emshotton/copperroute/benchmark/reports/plan9-t7t8-vs-java.md

# Comparison: java-current vs rs-main

Created 2026-09-03T23:23:26+00:00 from runs java-278fe14, plan9-t7t8. Config: threads=1 jobs=12 max_passes=10 timeout=300s seeds=1 time metric = cpu_s tier=pcbench

| candidate | version | sha |
|---|---|---|
| java-current | current | `278fe14123c4` |
| rs-main | — | `33b13d26ae10` |

## Overall

- **rs-main** vs java-current: **worse** — 394 wins, 211 losses (107 on hard metrics), 0 ties

## Per tier

| tier | candidate | wins | losses | ties | clean-pass rate | median Δscore | median time ratio |
|---|---|---|---|---|---|---|---|
| all | rs-main | 394 | 211 | 0 | 0.57 | +0.0 | 0.03 |
| d3-a | rs-main | 91 | 52 | 0 | 0.77 | 0.0 | 0.01 |
| d3-b | rs-main | 170 | 90 | 0 | 0.65 | +0.0 | 0.02 |
| d3-c | rs-main | 133 | 69 | 0 | 0.31 | +25.7 | 0.10 |
| pcbench | rs-main | 394 | 211 | 0 | 0.57 | +0.0 | 0.03 |

## Per board

| board | referee | candidate | clean | unrouted | viol | score | Δscore | noise | cpu s | Δcpu s | vias | length mm | verdict |
|---|---|---|---|---|---|---|---|---|---|---|---|---|---|
| pcbench-1-Wire-Wing-pcb_1-Wire_Wing | kicad | java-current | 1.00 | 0 | 0 | 1000.0 | | unmeasured | 46.5 | | 18 | 474.1 | baseline |
| pcbench-1-Wire-Wing-pcb_1-Wire_Wing | kicad | rs-main | 1.00 | 0 | 0 | 1000.0 | +0.0 | | 1.3 | -45.1 | 14 | 470.4 | win (score) |
| pcbench-16x12-bits-I2C_I2C_Servo | kicad | java-current | 0.00 | 0 | 53 | 905.4 | | unmeasured | 53.3 | | 46 | 1039.0 | baseline |
| pcbench-16x12-bits-I2C_I2C_Servo | kicad | rs-main | 1.00 | 0 | 0 | 1000.0 | +94.6 | | 1.6 | -51.7 | 41 | 1039.6 | win (clean_pass_rate) |
| pcbench-1Bitsy_1bitsy | kicad | java-current | 0.00 | 0 | 55 | 931.2 | | unmeasured | 355.2 | | 70 | 1042.8 | baseline |
| pcbench-1Bitsy_1bitsy | kicad | rs-main | 0.00 | 1 | 0 | 993.7 | +62.5 | | 52.5 | -302.7 | 69 | 1029.2 | loss (unrouted) |
| pcbench-2d_conduction_sk9822-matrix | kicad | java-current | 0.00 | 2 | 0 | 994.6 | | unmeasured | 354.9 | | 106 | 2776.3 | baseline |
| pcbench-2d_conduction_sk9822-matrix | kicad | rs-main | 0.00 | 2 | 0 | 994.6 | -0.0 | | 52.0 | -302.9 | 115 | 2768.8 | loss (score) |
| pcbench-4N35-TTL-Serial-Optoisolator_4N35-TTL-Serial-Optoisolator | kicad | java-current | 1.00 | 0 | 0 | 1000.0 | | unmeasured | 17.4 | | 0 | 219.9 | baseline |
| pcbench-4N35-TTL-Serial-Optoisolator_4N35-TTL-Serial-Optoisolator | kicad | rs-main | 1.00 | 0 | 0 | 1000.0 | +0.0 | | 0.2 | -17.3 | 0 | 219.6 | win (score) |
| pcbench-655_testboard | kicad | java-current | 1.00 | 0 | 0 | 1000.0 | | unmeasured | 71.0 | | 27 | 1002.1 | baseline |
| pcbench-655_testboard | kicad | rs-main | 1.00 | 0 | 0 | 1000.0 | +0.0 | | 2.7 | -68.3 | 26 | 1041.8 | win (score) |
| pcbench-6N137-TTL-Serial-Optoisolator_6N137-TTL-Serial-Optoisolator | kicad | java-current | 1.00 | 0 | 0 | 1000.0 | | unmeasured | 44.9 | | 0 | 277.3 | baseline |
| pcbench-6N137-TTL-Serial-Optoisolator_6N137-TTL-Serial-Optoisolator | kicad | rs-main | 0.00 | 1 | 0 | 964.3 | -35.7 | | 0.9 | -44.0 | 0 | 273.0 | loss (clean_pass_rate) |
| pcbench-6volt-5W-solar-cc_6vleadacidsolar | kicad | java-current | 0.00 | 0 | 12 | 980.2 | | unmeasured | 94.8 | | 19 | 949.6 | baseline |
| pcbench-6volt-5W-solar-cc_6vleadacidsolar | kicad | rs-main | 1.00 | 0 | 0 | 1000.0 | +19.8 | | 2.5 | -92.3 | 25 | 885.3 | win (clean_pass_rate) |
| pcbench-74Logic_SA_ADC_SA-ADC | kicad | java-current | 0.00 | 74 | 0 | 834.8 | | unmeasured | 383.7 | | 175 | 2981.5 | baseline |
| pcbench-74Logic_SA_ADC_SA-ADC | kicad | rs-main | 0.00 | 3 | 0 | 993.3 | +158.5 | | 228.2 | -155.4 | 199 | 4529.4 | win (unrouted) |
| pcbench-96boards-sensors_Sensors | kicad | java-current | 0.00 | 14 | 8 | 943.7 | | unmeasured | 394.2 | | 136 | 3334.9 | baseline |
| pcbench-96boards-sensors_Sensors | kicad | rs-main | 0.00 | 3 | 1 | 988.4 | +44.8 | | 112.9 | -281.3 | 157 | 3691.7 | win (unrouted) |
| pcbench-ABOVISP_ABOVISP | kicad | java-current | 0.00 | 1 | 7 | 922.6 | | unmeasured | 55.1 | | 5 | 196.6 | baseline |
| pcbench-ABOVISP_ABOVISP | kicad | rs-main | 1.00 | 0 | 0 | 1000.0 | +77.4 | | 1.1 | -53.9 | 3 | 193.0 | win (clean_pass_rate) |
| pcbench-ADC-PCM4202-SE_ADC-PCM4202-SE | kicad | java-current | 1.00 | 0 | 0 | 1000.0 | | unmeasured | 288.0 | | 41 | 2707.0 | baseline |
| pcbench-ADC-PCM4202-SE_ADC-PCM4202-SE | kicad | rs-main | 1.00 | 0 | 0 | 1000.0 | -0.0 | | 26.1 | -262.0 | 43 | 2641.6 | loss (score) |
| pcbench-APC_AtariPunkConsole | kicad | java-current | 1.00 | 0 | 0 | 1000.0 | | unmeasured | 29.2 | | 2 | 479.1 | baseline |
| pcbench-APC_AtariPunkConsole | kicad | rs-main | 1.00 | 0 | 0 | 1000.0 | -0.0 | | 0.1 | -29.1 | 2 | 484.6 | loss (score) |
| pcbench-APM-RPi-Shield_APM-RPi-Shield | kicad | java-current | 0.00 | 4 | 2 | 964.8 | | unmeasured | 203.5 | | 31 | 1346.1 | baseline |
| pcbench-APM-RPi-Shield_APM-RPi-Shield | kicad | rs-main | 0.00 | 7 | 1 | 942.4 | -22.4 | | 18.4 | -185.2 | 37 | 1180.0 | loss (unrouted) |
| pcbench-AS5043-Encoder_sensor-board | kicad | java-current | 0.00 | 0 | 2 | 986.7 | | unmeasured | 32.3 | | 9 | 249.7 | baseline |
| pcbench-AS5043-Encoder_sensor-board | kicad | rs-main | 1.00 | 0 | 0 | 1000.0 | +13.3 | | 0.3 | -32.0 | 9 | 246.9 | win (clean_pass_rate) |
| pcbench-ATmega32_ExploreUltraAvrDevKit_40pin_AVRMCU | kicad | java-current | 1.00 | 0 | 0 | 1000.0 | | unmeasured | 75.8 | | 7 | 1189.3 | baseline |
| pcbench-ATmega32_ExploreUltraAvrDevKit_40pin_AVRMCU | kicad | rs-main | 0.00 | 1 | 0 | 987.5 | -12.5 | | 3.2 | -72.6 | 7 | 1138.8 | loss (clean_pass_rate) |
| pcbench-ATtiny461Breakout_ATTiny461DevBoard | kicad | java-current | 0.00 | 1 | 2 | 963.2 | | unmeasured | 65.3 | | 3 | 296.4 | baseline |
| pcbench-ATtiny461Breakout_ATTiny461DevBoard | kicad | rs-main | 0.00 | 0 | 1 | 994.7 | +31.6 | | 0.2 | -65.1 | 3 | 283.5 | win (unrouted) |
| pcbench-AVR-ISP_level-shifter_AVR-ISP_level-shifter | kicad | java-current | 0.00 | 1 | 4 | 972.7 | | unmeasured | 83.2 | | 8 | 366.9 | baseline |
| pcbench-AVR-ISP_level-shifter_AVR-ISP_level-shifter | kicad | rs-main | 1.00 | 0 | 0 | 1000.0 | +27.3 | | 1.0 | -82.2 | 4 | 371.2 | win (clean_pass_rate) |
| pcbench-AVR-ISP_pogo-plug_1.27mm_AVR-ISP_pogo-plug_1.27mm | kicad | java-current | 1.00 | 0 | 0 | 1000.0 | | unmeasured | 44.2 | | 1 | 48.8 | baseline |
| pcbench-AVR-ISP_pogo-plug_1.27mm_AVR-ISP_pogo-plug_1.27mm | kicad | rs-main | 1.00 | 0 | 0 | 1000.0 | -0.0 | | 0.6 | -43.6 | 1 | 48.8 | loss (score) |
| pcbench-AVR-Playground_hello_world | kicad | java-current | 0.00 | 1 | 0 | 800.0 | | unmeasured | 26.6 | | 0 | 108.5 | baseline |
| pcbench-AVR-Playground_hello_world | kicad | rs-main | 0.00 | 1 | 0 | 800.0 | 0.0 | | 0.1 | -26.5 | 0 | 108.5 | win (cpu_s) |
| pcbench-AVR-ZIF-Programmer_AVR-ZIF-Prog | kicad | java-current | 1.00 | 0 | 0 | 1000.0 | | unmeasured | 104.0 | | 8 | 1490.5 | baseline |
| pcbench-AVR-ZIF-Programmer_AVR-ZIF-Prog | kicad | rs-main | 1.00 | 0 | 0 | 1000.0 | +0.0 | | 1.9 | -102.1 | 6 | 1502.7 | win (score) |
| pcbench-Amiga-A1012-PCB_Amiga-A1012 | kicad | java-current | 0.00 | 0 | 42 | 913.4 | | unmeasured | 107.4 | | 47 | 1745.1 | baseline |
| pcbench-Amiga-A1012-PCB_Amiga-A1012 | kicad | rs-main | 1.00 | 0 | 0 | 1000.0 | +86.6 | | 4.6 | -102.7 | 46 | 1764.4 | win (clean_pass_rate) |
| pcbench-AmpOne_dev-AmpOne | kicad | java-current | 0.00 | 1 | 0 | 996.9 | | unmeasured | 293.2 | | 60 | 2688.2 | baseline |
| pcbench-AmpOne_dev-AmpOne | kicad | rs-main | 1.00 | 0 | 0 | 1000.0 | +3.1 | | 18.2 | -275.0 | 46 | 2723.2 | win (clean_pass_rate) |
| pcbench-AnalogThermometer_AnalogThermometer | kicad | java-current | 0.00 | 0 | 3 | 982.9 | | unmeasured | 36.6 | | 2 | 208.7 | baseline |
| pcbench-AnalogThermometer_AnalogThermometer | kicad | rs-main | 1.00 | 0 | 0 | 1000.0 | +17.1 | | 0.4 | -36.2 | 4 | 207.6 | win (clean_pass_rate) |
| pcbench-Apple-M0110-BT_Apple M0110 | kicad | java-current | 1.00 | 0 | 0 | 1000.0 | | unmeasured | 155.5 | | 0 | 4384.2 | baseline |
| pcbench-Apple-M0110-BT_Apple M0110 | kicad | rs-main | 1.00 | 0 | 0 | 1000.0 | +0.0 | | 4.6 | -150.9 | 0 | 4364.1 | win (score) |
| pcbench-Arduino-Theremin_arduino-theremin-v1 | kicad | java-current | 0.00 | 1 | 0 | 963.0 | | unmeasured | 50.1 | | 3 | 596.6 | baseline |
| pcbench-Arduino-Theremin_arduino-theremin-v1 | kicad | rs-main | 0.00 | 2 | 0 | 925.9 | -37.0 | | 1.5 | -48.7 | 3 | 552.8 | loss (unrouted) |
| pcbench-Arduino_Lipo_Storage_Discharger_Lipo_Storage_Discharger | kicad | java-current | 1.00 | 0 | 0 | 1000.0 | | unmeasured | 64.0 | | 7 | 1041.8 | baseline |
| pcbench-Arduino_Lipo_Storage_Discharger_Lipo_Storage_Discharger | kicad | rs-main | 1.00 | 0 | 0 | 1000.0 | -0.0 | | 1.9 | -62.0 | 13 | 1041.7 | loss (score) |
| pcbench-Atmel-ICE-Header-Adapter_ice header adapter pcb | kicad | java-current | 0.00 | 3 | 0 | 957.7 | | unmeasured | 137.7 | | 0 | 970.9 | baseline |
| pcbench-Atmel-ICE-Header-Adapter_ice header adapter pcb | kicad | rs-main | 0.00 | 3 | 0 | 957.7 | +0.0 | | 5.7 | -132.0 | 0 | 916.2 | win (score) |
| pcbench-Avem_Hardware_Avem_demo | kicad | java-current | 0.00 | 1 | 39 | 890.0 | | unmeasured | 148.2 | | 16 | 656.7 | baseline |
| pcbench-Avem_Hardware_Avem_demo | kicad | rs-main | 1.00 | 0 | 0 | 1000.0 | +110.0 | | 2.6 | -145.6 | 20 | 717.4 | win (clean_pass_rate) |
| pcbench-AzizLight_AzizLight | kicad | java-current | 0.00 | 0 | 23 | 954.9 | | unmeasured | 93.0 | | 35 | 722.5 | baseline |
| pcbench-AzizLight_AzizLight | kicad | rs-main | 0.00 | 1 | 0 | 990.2 | +35.3 | | 4.6 | -88.5 | 45 | 704.6 | loss (unrouted) |
| pcbench-BB-PWR-3608_BB-PWR-3608_revA | kicad | java-current | 1.00 | 0 | 0 | 1000.0 | | unmeasured | 49.1 | | 3 | 94.3 | baseline |
| pcbench-BB-PWR-3608_BB-PWR-3608_revA | kicad | rs-main | 1.00 | 0 | 0 | 1000.0 | +0.0 | | 1.6 | -47.6 | 3 | 81.8 | win (score) |
| pcbench-BB-PWR-8009_BB-PWR-8009_revA | kicad | java-current | 1.00 | 0 | 0 | 1000.0 | | unmeasured | 59.9 | | 2 | 72.3 | baseline |
| pcbench-BB-PWR-8009_BB-PWR-8009_revA | kicad | rs-main | 1.00 | 0 | 0 | 1000.0 | +0.0 | | 1.0 | -58.9 | 0 | 76.3 | win (score) |
| pcbench-BLDC-controller_BLDC_controller | kicad | java-current | 0.00 | 134 | 46 | 674.5 | | unmeasured | 357.1 | | 44 | 863.4 | baseline |
| pcbench-BLDC-controller_BLDC_controller | kicad | rs-main | 0.00 | 18 | 1 | 958.6 | +284.1 | | 171.2 | -185.9 | 45 | 1285.6 | win (unrouted) |
| pcbench-BML-Badges_BML-Badges | kicad | java-current | 1.00 | 0 | 0 | 1000.0 | | unmeasured | 27.0 | | 0 | 460.8 | baseline |
| pcbench-BML-Badges_BML-Badges | kicad | rs-main | 1.00 | 0 | 0 | 1000.0 | -0.0 | | 0.1 | -26.8 | 0 | 470.8 | loss (score) |
| pcbench-BML-Badges_BML_01 | kicad | java-current | 1.00 | 0 | 0 | 1000.0 | | unmeasured | 19.9 | | 0 | 339.9 | baseline |
| pcbench-BML-Badges_BML_01 | kicad | rs-main | 1.00 | 0 | 0 | 1000.0 | -0.0 | | 0.2 | -19.7 | 0 | 346.2 | loss (score) |
| pcbench-Baofeng-Interface_BaofengInterfaceIsolated | kicad | java-current | 1.00 | 0 | 0 | 1000.0 | | unmeasured | 67.2 | | 0 | 668.8 | baseline |
| pcbench-Baofeng-Interface_BaofengInterfaceIsolated | kicad | rs-main | 1.00 | 0 | 0 | 1000.0 | -0.0 | | 2.3 | -64.9 | 0 | 679.4 | loss (score) |
| pcbench-BirdAttractor_BirdAttractor_RevA | kicad | java-current | 1.00 | 0 | 0 | 1000.0 | | unmeasured | 54.6 | | 2 | 374.0 | baseline |
| pcbench-BirdAttractor_BirdAttractor_RevA | kicad | rs-main | 1.00 | 0 | 0 | 1000.0 | +0.0 | | 3.2 | -51.5 | 2 | 361.4 | win (score) |
| pcbench-BirdAttractor_BirdAttractor_RevC | kicad | java-current | 1.00 | 0 | 0 | 1000.0 | | unmeasured | 68.6 | | 41 | 1085.6 | baseline |
| pcbench-BirdAttractor_BirdAttractor_RevC | kicad | rs-main | 1.00 | 0 | 0 | 1000.0 | +0.0 | | 2.7 | -65.9 | 38 | 1143.1 | win (score) |
| pcbench-BirthdayCakeKeyboard_10Key | kicad | java-current | 0.00 | 0 | 62 | 935.1 | | unmeasured | 269.9 | | 72 | 3894.3 | baseline |
| pcbench-BirthdayCakeKeyboard_10Key | kicad | rs-main | 0.00 | 1 | 0 | 994.8 | +59.7 | | 19.7 | -250.1 | 113 | 3817.4 | loss (unrouted) |
| pcbench-Biscay_Blueeye_mcu | kicad | java-current | 0.00 | 0 | 17 | 946.9 | | unmeasured | 81.0 | | 7 | 1169.7 | baseline |
| pcbench-Biscay_Blueeye_mcu | kicad | rs-main | 1.00 | 0 | 0 | 1000.0 | +53.1 | | 2.5 | -78.5 | 3 | 1232.1 | win (clean_pass_rate) |
| pcbench-Biscay_Blueeye_sipm-fpga | kicad | java-current | 0.00 | 2 | 77 | 884.0 | | unmeasured | 349.4 | | 26 | 1423.5 | baseline |
| pcbench-Biscay_Blueeye_sipm-fpga | kicad | rs-main | 0.00 | 2 | 0 | 986.7 | +102.7 | | 38.7 | -310.7 | 30 | 1371.0 | win (violations) |
| pcbench-Blink-Eras_AVR_ISP_Pogo | kicad | java-current | 1.00 | 0 | 0 | 1000.0 | | unmeasured | 13.5 | | 0 | 97.0 | baseline |
| pcbench-Blink-Eras_AVR_ISP_Pogo | kicad | rs-main | 1.00 | 0 | 0 | 1000.0 | 0.0 | | 0.0 | -13.5 | 0 | 97.0 | win (cpu_s) |
| pcbench-Box0-hv-analog-breakoutboard_breakout | kicad | java-current | 0.00 | 128 | 0 | 174.2 | | unmeasured | 254.5 | | 0 | 98.2 | baseline |
| pcbench-Box0-hv-analog-breakoutboard_breakout | kicad | rs-main | 0.00 | 128 | 0 | 174.2 | 0.0 | | 27.9 | -226.6 | 0 | 98.2 | win (cpu_s) |
| pcbench-Brushless_ESC_Brushless_ESC | kicad | java-current | 0.00 | 1 | 69 | 908.6 | | unmeasured | 171.9 | | 74 | 1377.5 | baseline |
| pcbench-Brushless_ESC_Brushless_ESC | kicad | rs-main | 0.00 | 1 | 14 | 976.5 | +67.9 | | 15.9 | -156.0 | 71 | 1343.1 | win (violations) |
| pcbench-C-BISCUIT_crowbar | kicad | java-current | 0.00 | 0 | 3 | 966.7 | | unmeasured | 22.2 | | 5 | 145.5 | baseline |
| pcbench-C-BISCUIT_crowbar | kicad | rs-main | 1.00 | 0 | 0 | 1000.0 | +33.3 | | 0.2 | -22.0 | 5 | 142.2 | win (clean_pass_rate) |
| pcbench-CAL430FR_CAL430F | kicad | java-current | 0.00 | 8 | 28 | 852.2 | | unmeasured | 375.7 | | 63 | 1012.4 | baseline |
| pcbench-CAL430FR_CAL430F | kicad | rs-main | 0.00 | 8 | 0 | 913.0 | +60.9 | | 67.3 | -308.3 | 62 | 1058.4 | win (violations) |
| pcbench-CAL430FR_CAL430F_watch | kicad | java-current | 0.00 | 0 | 18 | 836.4 | | unmeasured | 52.7 | | 9 | 389.8 | baseline |
| pcbench-CAL430FR_CAL430F_watch | kicad | rs-main | 1.00 | 0 | 0 | 1000.0 | +163.6 | | 1.9 | -50.8 | 8 | 380.8 | win (clean_pass_rate) |
| pcbench-CapPCB_CapPcb | kicad | java-current | 1.00 | 0 | 0 | 1000.0 | | unmeasured | 26.4 | | 0 | 85.3 | baseline |
| pcbench-CapPCB_CapPcb | kicad | rs-main | 1.00 | 0 | 0 | 1000.0 | +0.0 | | 1.2 | -25.2 | 0 | 73.9 | win (score) |
| pcbench-Cherry-Mx-Bitboard_Cherry Mx Bitboard | kicad | java-current | 1.00 | 0 | 0 | 1000.0 | | unmeasured | 12.8 | | 0 | 72.5 | baseline |
| pcbench-Cherry-Mx-Bitboard_Cherry Mx Bitboard | kicad | rs-main | 1.00 | 0 | 0 | 1000.0 | 0.0 | | 0.0 | -12.8 | 0 | 72.5 | win (cpu_s) |
| pcbench-ChirpHardware_chirp | kicad | java-current | 0.00 | 1 | 65 | 860.0 | | unmeasured | 202.8 | | 31 | 763.5 | baseline |
| pcbench-ChirpHardware_chirp | kicad | rs-main | 1.00 | 0 | 0 | 1000.0 | +140.0 | | 56.0 | -146.8 | 25 | 760.2 | win (clean_pass_rate) |
| pcbench-CompactFlashBreakout_CompactFlashBreakout | kicad | java-current | 0.00 | 0 | 1 | 993.9 | | unmeasured | 97.3 | | 16 | 479.8 | baseline |
| pcbench-CompactFlashBreakout_CompactFlashBreakout | kicad | rs-main | 1.00 | 0 | 0 | 1000.0 | +6.1 | | 2.4 | -94.9 | 17 | 460.0 | win (clean_pass_rate) |
| pcbench-CoreOne-xCORE200-Original_CoreOne | kicad | java-current | 0.00 | 302 | 3 | 629.2 | | unmeasured | 366.1 | | 269 | 2530.7 | baseline |
| pcbench-CoreOne-xCORE200-Original_CoreOne | kicad | rs-main | 0.00 | 57 | 1 | 929.9 | +300.7 | | 306.3 | -59.8 | 294 | 5943.2 | win (unrouted) |
| pcbench-CubeSAT-Reaction-Wheel_Edison_Motor_Servo | kicad | java-current | 1.00 | 0 | 0 | 1000.0 | | unmeasured | 16.5 | | 0 | 115.7 | baseline |
| pcbench-CubeSAT-Reaction-Wheel_Edison_Motor_Servo | kicad | rs-main | 1.00 | 0 | 0 | 1000.0 | 0.0 | | 0.1 | -16.3 | 0 | 115.7 | win (cpu_s) |
| pcbench-CubeSAT-Reaction-Wheel__autosave-GPIO to motor | kicad | java-current | 1.00 | 0 | 0 | 1000.0 | | unmeasured | 66.0 | | 3 | 673.2 | baseline |
| pcbench-CubeSAT-Reaction-Wheel__autosave-GPIO to motor | kicad | rs-main | 1.00 | 0 | 0 | 1000.0 | -0.0 | | 0.9 | -65.0 | 4 | 665.3 | loss (score) |
| pcbench-Curryboard_Curryboard | kicad | java-current | 0.00 | 3 | 0 | 980.3 | | unmeasured | 366.6 | | 79 | 1825.5 | baseline |
| pcbench-Curryboard_Curryboard | kicad | rs-main | 0.00 | 1 | 0 | 993.4 | +13.2 | | 43.5 | -323.1 | 70 | 1943.1 | win (unrouted) |
| pcbench-DAC-ADAU1966_DAC-ADAU1966 | kicad | java-current | 0.00 | 102 | 0 | 836.3 | | unmeasured | 374.5 | | 129 | 3150.1 | baseline |
| pcbench-DAC-ADAU1966_DAC-ADAU1966 | kicad | rs-main | 0.00 | 1 | 0 | 998.4 | +162.1 | | 150.7 | -223.8 | 132 | 3914.8 | win (unrouted) |
| pcbench-DC25_DC25 | kicad | java-current | 0.00 | 0 | 25 | 927.5 | | unmeasured | 133.2 | | 46 | 1506.4 | baseline |
| pcbench-DC25_DC25 | kicad | rs-main | 0.00 | 0 | 4 | 988.4 | +60.9 | | 6.5 | -126.7 | 47 | 1449.1 | win (violations) |
| pcbench-DIYDAC_DIYDAC | kicad | java-current | 1.00 | 0 | 0 | 1000.0 | | unmeasured | 17.8 | | 0 | 68.1 | baseline |
| pcbench-DIYDAC_DIYDAC | kicad | rs-main | 1.00 | 0 | 0 | 1000.0 | 0.0 | | 0.1 | -17.7 | 0 | 68.1 | win (cpu_s) |
| pcbench-DPS-1200FB_Adapter_Adapter | kicad | java-current | 0.00 | 1 | 3 | 987.2 | | unmeasured | 88.0 | | 0 | 796.0 | baseline |
| pcbench-DPS-1200FB_Adapter_Adapter | kicad | rs-main | 0.00 | 1 | 3 | 987.2 | +0.0 | | 1.9 | -86.0 | 0 | 794.8 | win (score) |
| pcbench-DaWeather---Project__autosave-CarteDaWeather | kicad | java-current | 1.00 | 0 | 0 | 1000.0 | | unmeasured | 32.4 | | 0 | 594.9 | baseline |
| pcbench-DaWeather---Project__autosave-CarteDaWeather | kicad | rs-main | 0.00 | 0 | 1 | 995.3 | -4.7 | | 0.3 | -32.1 | 0 | 601.2 | loss (clean_pass_rate) |
| pcbench-DasBlinkinput_Das Blinkinput | kicad | java-current | 1.00 | 0 | 0 | 1000.0 | | unmeasured | 340.6 | | 20 | 652.1 | baseline |
| pcbench-DasBlinkinput_Das Blinkinput | kicad | rs-main | 1.00 | 0 | 0 | 1000.0 | +0.0 | | 56.8 | -283.8 | 18 | 668.2 | win (score) |
| pcbench-Dekada_dekada | kicad | java-current | 1.00 | 0 | 0 | 1000.0 | | unmeasured | 148.2 | | 0 | 379.8 | baseline |
| pcbench-Dekada_dekada | kicad | rs-main | 1.00 | 0 | 0 | 1000.0 | +0.0 | | 14.2 | -133.9 | 0 | 379.8 | win (score) |
| pcbench-Dekada_dekada_TopoR_curves | kicad | java-current | 1.00 | 0 | 0 | 1000.0 | | unmeasured | 146.5 | | 0 | 379.8 | baseline |
| pcbench-Dekada_dekada_TopoR_curves | kicad | rs-main | 1.00 | 0 | 0 | 1000.0 | +0.0 | | 8.5 | -138.0 | 0 | 379.8 | win (score) |
| pcbench-DerKnopf_digi-pot | kicad | java-current | 0.00 | 1 | 54 | 821.2 | | unmeasured | 204.7 | | 29 | 462.4 | baseline |
| pcbench-DerKnopf_digi-pot | kicad | rs-main | 0.00 | 2 | 0 | 969.7 | +148.5 | | 10.9 | -193.8 | 27 | 463.2 | loss (unrouted) |
| pcbench-DerKnopf_led-ring | kicad | java-current | 0.00 | 0 | 4 | 988.4 | | unmeasured | 206.5 | | 45 | 569.4 | baseline |
| pcbench-DerKnopf_led-ring | kicad | rs-main | 1.00 | 0 | 0 | 1000.0 | +11.6 | | 11.0 | -195.5 | 44 | 557.8 | win (clean_pass_rate) |
| pcbench-DerKnopf_power-supply | kicad | java-current | 1.00 | 0 | 0 | 1000.0 | | unmeasured | 70.1 | | 1 | 185.7 | baseline |
| pcbench-DerKnopf_power-supply | kicad | rs-main | 1.00 | 0 | 0 | 1000.0 | -0.0 | | 1.5 | -68.6 | 1 | 188.9 | loss (score) |
| pcbench-DiscoDanceFloorV1_DiscoDongle | kicad | java-current | 0.00 | 0 | 11 | 958.5 | | unmeasured | 284.7 | | 10 | 519.2 | baseline |
| pcbench-DiscoDanceFloorV1_DiscoDongle | kicad | rs-main | 1.00 | 0 | 0 | 1000.0 | +41.5 | | 16.4 | -268.3 | 6 | 550.6 | win (clean_pass_rate) |
| pcbench-DoroidOscillo-Board_Android_Oscilloscope | kicad | java-current | 0.00 | 13 | 67 | 914.6 | | unmeasured | 336.3 | | 102 | 1636.5 | baseline |
| pcbench-DoroidOscillo-Board_Android_Oscilloscope | kicad | rs-main | 0.00 | 6 | 0 | 980.6 | +66.0 | | 137.8 | -198.5 | 96 | 1753.4 | win (unrouted) |
| pcbench-DualLM317BenchSupply_DualLM317BenchSupply | kicad | java-current | 1.00 | 0 | 0 | 1000.0 | | unmeasured | 101.3 | | 0 | 1139.7 | baseline |
| pcbench-DualLM317BenchSupply_DualLM317BenchSupply | kicad | rs-main | 1.00 | 0 | 0 | 1000.0 | -0.0 | | 4.6 | -96.7 | 0 | 1142.6 | loss (score) |
| pcbench-DustSensorShield_DustSensorShield | kicad | java-current | 0.00 | 1 | 0 | 941.2 | | unmeasured | 69.4 | | 6 | 467.2 | baseline |
| pcbench-DustSensorShield_DustSensorShield | kicad | rs-main | 0.00 | 1 | 0 | 941.2 | -0.0 | | 1.2 | -68.2 | 12 | 453.3 | loss (score) |
| pcbench-E202VAR-Natural-Radio-Receiver_e202var-vlf-radio-receiver | kicad | java-current | 0.00 | 1 | 0 | 989.1 | | unmeasured | 77.6 | | 1 | 961.2 | baseline |
| pcbench-E202VAR-Natural-Radio-Receiver_e202var-vlf-radio-receiver | kicad | rs-main | 0.00 | 1 | 0 | 989.1 | -0.0 | | 2.7 | -74.9 | 1 | 990.2 | loss (score) |
| pcbench-ESP-12-breakout_ESP12E-breakout | kicad | java-current | 1.00 | 0 | 0 | 1000.0 | | unmeasured | 47.7 | | 9 | 310.7 | baseline |
| pcbench-ESP-12-breakout_ESP12E-breakout | kicad | rs-main | 1.00 | 0 | 0 | 1000.0 | +0.0 | | 0.5 | -47.2 | 7 | 316.0 | win (score) |
| pcbench-ESP-Breakout_ESP-Breakout | kicad | java-current | 1.00 | 0 | 0 | 1000.0 | | unmeasured | 41.5 | | 18 | 350.8 | baseline |
| pcbench-ESP-Breakout_ESP-Breakout | kicad | rs-main | 1.00 | 0 | 0 | 1000.0 | +0.0 | | 0.4 | -41.1 | 17 | 360.1 | win (score) |
| pcbench-ESP07-Breakout_ESP07-Breakout | kicad | java-current | 0.00 | 2 | 0 | 969.2 | | unmeasured | 116.8 | | 10 | 702.2 | baseline |
| pcbench-ESP07-Breakout_ESP07-Breakout | kicad | rs-main | 0.00 | 3 | 3 | 944.6 | -24.6 | | 4.0 | -112.9 | 11 | 717.6 | loss (unrouted) |
| pcbench-ESP32-Module-Breakout_ESP32S-breakout | kicad | java-current | 0.00 | 0 | 13 | 943.5 | | unmeasured | 83.6 | | 27 | 750.3 | baseline |
| pcbench-ESP32-Module-Breakout_ESP32S-breakout | kicad | rs-main | 1.00 | 0 | 0 | 1000.0 | +56.5 | | 2.0 | -81.7 | 29 | 745.2 | win (clean_pass_rate) |
| pcbench-ESP8266-MQTT-battery-monitor-hw_battery-monitor | kicad | java-current | 0.00 | 0 | 27 | 943.2 | | unmeasured | 87.5 | | 25 | 645.7 | baseline |
| pcbench-ESP8266-MQTT-battery-monitor-hw_battery-monitor | kicad | rs-main | 0.00 | 1 | 0 | 989.5 | +46.3 | | 5.3 | -82.2 | 24 | 622.0 | loss (unrouted) |
| pcbench-ESPLux_Board | kicad | java-current | 1.00 | 0 | 0 | 1000.0 | | unmeasured | 270.2 | | 10 | 789.9 | baseline |
| pcbench-ESPLux_Board | kicad | rs-main | 0.00 | 1 | 0 | 981.5 | -18.5 | | 4.3 | -266.0 | 26 | 795.1 | loss (clean_pass_rate) |
| pcbench-ESP_BaPoTeSta_ESP_BaPoTeSta | kicad | java-current | 0.00 | 2 | 0 | 981.5 | | unmeasured | 166.0 | | 32 | 791.0 | baseline |
| pcbench-ESP_BaPoTeSta_ESP_BaPoTeSta | kicad | rs-main | 0.00 | 9 | 0 | 916.7 | -64.8 | | 13.2 | -152.8 | 16 | 699.5 | loss (unrouted) |
| pcbench-ESP_WiFiSwitch_WifiSwitch | kicad | java-current | 0.00 | 0 | 1 | 990.9 | | unmeasured | 37.6 | | 6 | 323.1 | baseline |
| pcbench-ESP_WiFiSwitch_WifiSwitch | kicad | rs-main | 1.00 | 0 | 0 | 1000.0 | +9.1 | | 0.3 | -37.2 | 7 | 320.7 | win (clean_pass_rate) |
| pcbench-Eggbot-Spherebot-polargraph-Controller_eggbot-spherebot-polargraph-controller | kicad | java-current | 1.00 | 0 | 0 | 1000.0 | | unmeasured | 56.5 | | 3 | 1268.6 | baseline |
| pcbench-Eggbot-Spherebot-polargraph-Controller_eggbot-spherebot-polargraph-controller | kicad | rs-main | 1.00 | 0 | 0 | 1000.0 | -0.0 | | 0.8 | -55.6 | 4 | 1270.7 | loss (score) |
| pcbench-Electronics-MainBoard_MainBoard | kicad | java-current | 0.00 | 1 | 42 | 967.0 | | unmeasured | 336.6 | | 84 | 2899.8 | baseline |
| pcbench-Electronics-MainBoard_MainBoard | kicad | rs-main | 0.00 | 1 | 0 | 996.5 | +29.5 | | 26.2 | -310.4 | 85 | 2898.4 | win (violations) |
| pcbench-EncoderBoard_Enc_Pan_Led | kicad | java-current | 0.00 | 7 | 26 | 874.2 | | unmeasured | 349.3 | | 38 | 840.4 | baseline |
| pcbench-EncoderBoard_Enc_Pan_Led | kicad | rs-main | 0.00 | 11 | 0 | 886.6 | +12.4 | | 27.2 | -322.1 | 26 | 743.3 | loss (unrouted) |
| pcbench-FRM16_Relay_Module_I2C_Controller_relay_controller | kicad | java-current | 0.00 | 0 | 3 | 989.1 | | unmeasured | 302.2 | | 52 | 1478.1 | baseline |
| pcbench-FRM16_Relay_Module_I2C_Controller_relay_controller | kicad | rs-main | 0.00 | 1 | 0 | 981.8 | -7.3 | | 8.3 | -293.9 | 61 | 1532.8 | loss (unrouted) |
| pcbench-FT231X_breakout_FTDI_FT231XS-U_Breakout | kicad | java-current | 0.00 | 3 | 3 | 910.0 | | unmeasured | 130.3 | | 17 | 371.3 | baseline |
| pcbench-FT231X_breakout_FTDI_FT231XS-U_Breakout | kicad | rs-main | 0.00 | 1 | 0 | 975.0 | +65.0 | | 3.8 | -126.5 | 16 | 400.0 | win (unrouted) |
| pcbench-FlashProgrammer_flash_programmer | kicad | java-current | 0.00 | 5 | 52 | 890.8 | | unmeasured | 331.7 | | 60 | 1453.3 | baseline |
| pcbench-FlashProgrammer_flash_programmer | kicad | rs-main | 0.00 | 4 | 0 | 971.6 | +80.9 | | 24.1 | -307.6 | 56 | 1441.7 | win (unrouted) |
| pcbench-FogDrive_attiny45_slim | kicad | java-current | 1.00 | 0 | 0 | 1000.0 | | unmeasured | 17.9 | | 0 | 52.5 | baseline |
| pcbench-FogDrive_attiny45_slim | kicad | rs-main | 1.00 | 0 | 0 | 1000.0 | 0.0 | | 0.1 | -17.8 | 0 | 52.5 | win (cpu_s) |
| pcbench-HES-V2__autosave-hes | kicad | java-current | 1.00 | 0 | 0 | 1000.0 | | unmeasured | 30.7 | | 0 | 456.9 | baseline |
| pcbench-HES-V2__autosave-hes | kicad | rs-main | 1.00 | 0 | 0 | 1000.0 | +0.0 | | 0.1 | -30.6 | 0 | 456.2 | win (score) |
| pcbench-HES-V2_hes | kicad | java-current | 1.00 | 0 | 0 | 1000.0 | | unmeasured | 30.0 | | 0 | 456.9 | baseline |
| pcbench-HES-V2_hes | kicad | rs-main | 1.00 | 0 | 0 | 1000.0 | +0.0 | | 0.1 | -29.9 | 0 | 456.2 | win (score) |
| pcbench-HW-AC-Emeter_ac-power-monitor | kicad | java-current | 0.00 | 1 | 13 | 966.3 | | unmeasured | 157.8 | | 37 | 1110.7 | baseline |
| pcbench-HW-AC-Emeter_ac-power-monitor | kicad | rs-main | 1.00 | 0 | 0 | 1000.0 | +33.6 | | 5.9 | -151.9 | 35 | 1196.2 | win (clean_pass_rate) |
| pcbench-Hangul-Clock_Hangul | kicad | java-current | 0.00 | 0 | 28 | 973.2 | | unmeasured | 274.8 | | 73 | 3221.7 | baseline |
| pcbench-Hangul-Clock_Hangul | kicad | rs-main | 1.00 | 0 | 0 | 1000.0 | +26.8 | | 18.4 | -256.4 | 81 | 3240.4 | win (clean_pass_rate) |
| pcbench-Hardware-done-with-kicad_AVRlearn | kicad | java-current | 0.00 | 0 | 3 | 976.0 | | unmeasured | 29.9 | | 8 | 415.6 | baseline |
| pcbench-Hardware-done-with-kicad_AVRlearn | kicad | rs-main | 1.00 | 0 | 0 | 1000.0 | +24.0 | | 0.3 | -29.6 | 7 | 424.8 | win (clean_pass_rate) |
| pcbench-Hardware_Playground_BL_PCB_latest | kicad | java-current | 0.00 | 0 | 24 | 979.9 | | unmeasured | 158.5 | | 16 | 1888.5 | baseline |
| pcbench-Hardware_Playground_BL_PCB_latest | kicad | rs-main | 1.00 | 0 | 0 | 1000.0 | +20.1 | | 9.3 | -149.1 | 16 | 1865.9 | win (clean_pass_rate) |
| pcbench-Hardware_Playground_Touch_Switch_1ch_PCB | kicad | java-current | 0.00 | 1 | 19 | 955.1 | | unmeasured | 285.4 | | 29 | 668.1 | baseline |
| pcbench-Hardware_Playground_Touch_Switch_1ch_PCB | kicad | rs-main | 0.00 | 3 | 0 | 972.0 | +16.8 | | 24.9 | -260.6 | 28 | 711.8 | loss (unrouted) |
| pcbench-Hardware_Playground_buck_led_driver | kicad | java-current | 0.00 | 1 | 0 | 944.4 | | unmeasured | 34.8 | | 3 | 104.1 | baseline |
| pcbench-Hardware_Playground_buck_led_driver | kicad | rs-main | 0.00 | 1 | 0 | 944.4 | -0.0 | | 0.4 | -34.4 | 3 | 105.2 | loss (score) |
| pcbench-Hardware_Playground_esp8266_uno_relay | kicad | java-current | 0.00 | 1 | 0 | 994.9 | | unmeasured | 116.6 | | 1 | 580.2 | baseline |
| pcbench-Hardware_Playground_esp8266_uno_relay | kicad | rs-main | 0.00 | 1 | 0 | 994.9 | -0.0 | | 5.8 | -110.8 | 1 | 594.5 | loss (score) |
| pcbench-Hardware_Playground_hy_adapter | kicad | java-current | 1.00 | 0 | 0 | 1000.0 | | unmeasured | 67.3 | | 7 | 73.1 | baseline |
| pcbench-Hardware_Playground_hy_adapter | kicad | rs-main | 1.00 | 0 | 0 | 1000.0 | -0.0 | | 1.9 | -65.4 | 9 | 62.1 | loss (score) |
| pcbench-Hardware_Playground_minimal_node_rfm69w | kicad | java-current | 0.00 | 9 | 8 | 897.1 | | unmeasured | 263.8 | | 22 | 473.1 | baseline |
| pcbench-Hardware_Playground_minimal_node_rfm69w | kicad | rs-main | 0.00 | 6 | 0 | 941.7 | +44.7 | | 17.0 | -246.8 | 30 | 526.9 | win (unrouted) |
| pcbench-Hardware_Playground_nrf52832_uno | kicad | java-current | 0.00 | 4 | 36 | 883.3 | | unmeasured | 280.3 | | 27 | 1402.3 | baseline |
| pcbench-Hardware_Playground_nrf52832_uno | kicad | rs-main | 0.00 | 5 | 0 | 947.9 | +64.6 | | 22.6 | -257.7 | 33 | 1432.8 | loss (unrouted) |
| pcbench-Hardware_Playground_orange_pi_zero_node | kicad | java-current | 0.00 | 1 | 2 | 993.1 | | unmeasured | 153.1 | | 1 | 781.5 | baseline |
| pcbench-Hardware_Playground_orange_pi_zero_node | kicad | rs-main | 0.00 | 1 | 1 | 994.1 | +1.0 | | 10.0 | -143.1 | 1 | 779.2 | win (violations) |
| pcbench-Hardware_Playground_pro_mini | kicad | java-current | 0.00 | 1 | 0 | 987.2 | | unmeasured | 131.0 | | 4 | 462.4 | baseline |
| pcbench-Hardware_Playground_pro_mini | kicad | rs-main | 0.00 | 3 | 0 | 961.5 | -25.6 | | 7.2 | -123.9 | 5 | 417.9 | loss (unrouted) |
| pcbench-Hardware_Playground_rpi_zero | kicad | java-current | 0.00 | 2 | 21 | 971.4 | | unmeasured | 193.6 | | 11 | 845.8 | baseline |
| pcbench-Hardware_Playground_rpi_zero | kicad | rs-main | 0.00 | 1 | 13 | 983.4 | +12.0 | | 16.8 | -176.7 | 14 | 867.1 | win (unrouted) |
| pcbench-Hardware_Playground_serial_gw_ATMEGA328P | kicad | java-current | 0.00 | 1 | 57 | 928.7 | | unmeasured | 338.0 | | 44 | 779.4 | baseline |
| pcbench-Hardware_Playground_serial_gw_ATMEGA328P | kicad | rs-main | 0.00 | 1 | 10 | 982.8 | +54.0 | | 40.3 | -297.7 | 34 | 778.9 | win (violations) |
| pcbench-Hardware_Playground_serial_gw_maple_mini | kicad | java-current | 1.00 | 0 | 0 | 1000.0 | | unmeasured | 125.3 | | 7 | 925.2 | baseline |
| pcbench-Hardware_Playground_serial_gw_maple_mini | kicad | rs-main | 1.00 | 0 | 0 | 1000.0 | +0.0 | | 6.1 | -119.2 | 6 | 924.0 | win (score) |
| pcbench-Hardware_Playground_usb_shield | kicad | java-current | 1.00 | 0 | 0 | 1000.0 | | unmeasured | 126.7 | | 0 | 703.6 | baseline |
| pcbench-Hardware_Playground_usb_shield | kicad | rs-main | 0.00 | 1 | 0 | 995.3 | -4.7 | | 13.0 | -113.7 | 1 | 673.2 | loss (clean_pass_rate) |
| pcbench-Hardware_Playground_wifi_lights | kicad | java-current | 1.00 | 0 | 0 | 1000.0 | | unmeasured | 70.7 | | 8 | 628.4 | baseline |
| pcbench-Hardware_Playground_wifi_lights | kicad | rs-main | 1.00 | 0 | 0 | 1000.0 | +0.0 | | 0.8 | -69.8 | 7 | 617.0 | win (score) |
| pcbench-HaveSome_PCB_HaveSomePCB | kicad | java-current | 0.00 | 1 | 0 | 956.5 | | unmeasured | 66.7 | | 0 | 74.2 | baseline |
| pcbench-HaveSome_PCB_HaveSomePCB | kicad | rs-main | 1.00 | 0 | 0 | 1000.0 | +43.5 | | 1.6 | -65.1 | 1 | 82.9 | win (clean_pass_rate) |
| pcbench-HellScribe_HellScribe | kicad | java-current | 0.00 | 0 | 25 | 946.2 | | unmeasured | 105.8 | | 47 | 1541.4 | baseline |
| pcbench-HellScribe_HellScribe | kicad | rs-main | 1.00 | 0 | 0 | 1000.0 | +53.8 | | 4.6 | -101.2 | 44 | 1562.3 | win (clean_pass_rate) |
| pcbench-HillhacksLantern_LEDLantern | kicad | java-current | 0.00 | 2 | 0 | 928.6 | | unmeasured | 52.0 | | 2 | 379.4 | baseline |
| pcbench-HillhacksLantern_LEDLantern | kicad | rs-main | 0.00 | 3 | 0 | 892.9 | -35.7 | | 1.2 | -50.8 | 3 | 379.2 | loss (unrouted) |
| pcbench-Hypfer-RGB-W-LED-Controller_led_strip_controller | kicad | java-current | 0.00 | 1 | 0 | 986.5 | | unmeasured | 88.3 | | 0 | 1093.1 | baseline |
| pcbench-Hypfer-RGB-W-LED-Controller_led_strip_controller | kicad | rs-main | 1.00 | 0 | 0 | 1000.0 | +13.5 | | 2.0 | -86.3 | 0 | 1199.6 | win (clean_pass_rate) |
| pcbench-I2CTempsensor_sensors | kicad | java-current | 1.00 | 0 | 0 | 1000.0 | | unmeasured | 16.2 | | 0 | 142.5 | baseline |
| pcbench-I2CTempsensor_sensors | kicad | rs-main | 1.00 | 0 | 0 | 1000.0 | -0.0 | | 0.1 | -16.1 | 0 | 152.9 | loss (score) |
| pcbench-ID-FIX_scanConnect | kicad | java-current | 1.00 | 0 | 0 | 1000.0 | | unmeasured | 12.5 | | 0 | 50.5 | baseline |
| pcbench-ID-FIX_scanConnect | kicad | rs-main | 1.00 | 0 | 0 | 1000.0 | -0.0 | | 0.0 | -12.5 | 0 | 51.9 | loss (score) |
| pcbench-IR-Transponder-ATTiny85-v2_Transponder_v2 | kicad | java-current | 0.00 | 1 | 0 | 952.4 | | unmeasured | 31.4 | | 3 | 130.4 | baseline |
| pcbench-IR-Transponder-ATTiny85-v2_Transponder_v2 | kicad | rs-main | 0.00 | 1 | 0 | 952.4 | +0.0 | | 0.8 | -30.6 | 2 | 121.8 | win (score) |
| pcbench-ISO-port_ch340-usb-serial-isolated | kicad | java-current | 0.00 | 1 | 0 | 987.3 | | unmeasured | 101.5 | | 20 | 661.3 | baseline |
| pcbench-ISO-port_ch340-usb-serial-isolated | kicad | rs-main | 0.00 | 1 | 0 | 987.3 | +0.0 | | 9.2 | -92.2 | 20 | 645.5 | win (score) |
| pcbench-Inhibition_amplifier | kicad | java-current | 1.00 | 0 | 0 | 1000.0 | | unmeasured | 243.2 | | 9 | 2386.8 | baseline |
| pcbench-Inhibition_amplifier | kicad | rs-main | 0.00 | 2 | 0 | 986.7 | -13.3 | | 6.8 | -236.3 | 8 | 2237.0 | loss (clean_pass_rate) |
| pcbench-Inkjet_InkjetBreakout | kicad | java-current | 0.00 | 0 | 21 | 676.9 | | unmeasured | 27.0 | | 3 | 252.6 | baseline |
| pcbench-Inkjet_InkjetBreakout | kicad | rs-main | 1.00 | 0 | 0 | 1000.0 | +323.1 | | 0.2 | -26.8 | 3 | 254.7 | win (clean_pass_rate) |
| pcbench-Inkjet_InkjetDriver | kicad | java-current | 0.00 | 0 | 6 | 981.5 | | unmeasured | 83.1 | | 28 | 1179.4 | baseline |
| pcbench-Inkjet_InkjetDriver | kicad | rs-main | 1.00 | 0 | 0 | 1000.0 | +18.5 | | 2.3 | -80.8 | 30 | 1201.5 | win (clean_pass_rate) |
| pcbench-Inkjet_PiezoDriver | kicad | java-current | 0.00 | 1 | 9 | 903.4 | | unmeasured | 61.4 | | 9 | 265.7 | baseline |
| pcbench-Inkjet_PiezoDriver | kicad | rs-main | 0.00 | 1 | 0 | 965.5 | +62.1 | | 3.5 | -57.9 | 7 | 258.9 | win (violations) |
| pcbench-Inkjet__autosave-InkjetDriver | kicad | java-current | 0.00 | 0 | 6 | 981.5 | | unmeasured | 85.0 | | 28 | 1179.4 | baseline |
| pcbench-Inkjet__autosave-InkjetDriver | kicad | rs-main | 1.00 | 0 | 0 | 1000.0 | +18.5 | | 3.6 | -81.4 | 30 | 1201.5 | win (clean_pass_rate) |
| pcbench-JLink-SWD_JLink-SWD | kicad | java-current | 1.00 | 0 | 0 | 1000.0 | | unmeasured | 44.7 | | 4 | 298.0 | baseline |
| pcbench-JLink-SWD_JLink-SWD | kicad | rs-main | 1.00 | 0 | 0 | 1000.0 | -0.0 | | 0.6 | -44.0 | 5 | 304.6 | loss (score) |
| pcbench-Kefersender_UKW TX | kicad | java-current | 0.00 | 6 | 8 | 912.6 | | unmeasured | 135.6 | | 0 | 416.9 | baseline |
| pcbench-Kefersender_UKW TX | kicad | rs-main | 0.00 | 6 | 0 | 931.0 | +18.4 | | 9.7 | -125.9 | 0 | 393.5 | win (violations) |
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
