emshotton/copperroute/crates/copper-drc/tests/data/solder-mask-unnumbered-pads/README.md

# Logical pad identity oracle

Both physical pads have empty pad numbers in the same footprint; they are not one logical pad. Both are unnetted. KiCad 10.0.6 reports 1 mask bridges. Derived from solder-mask-pad-pad with net assignments removed and pad numbers changed.

```sh
kicad-cli pcb drc --format json --all-track-errors -o drc.json mask.kicad_pcb
```

The Rust test models the browser adapter splitting physical pads into independently placed components, preserving their source footprint and source pad number.
