emshotton/copperroute/tests/reference-frozen/java-head-2026-09/router-dac2020-bm01/router-steps18.meta.txt

jar          <FREEROUTING_JAVA_DIR>/build/libs/freerouting-current-executable.jar
jar size     63288652 bytes
jar mtime    2026-08-29 08:05:35 -0700
jar version  Freerouting 2.3.1-SNAPSHOT
java         openjdk version "25.0.4.1" 2026-08-18
hash mode    -XX:hashCode=2
driver       <workspace>/scripts/differential/java/P6T1.java --steps=1-8
connections  294
command      java -Djava.awt.headless=true -Duser.language=en -Duser.country=US -XX:+UnlockExperimentalVMOptions -XX:hashCode=2 -cp <classes>:<jar> app.freerouting.autoroute.maze.P6T1 <FREEROUTING_JAVA_DIR>/fixtures/Issue508-DAC2020_bm01.dsn 100000 1 - 1-8 0
header       HEADER jar=<FREEROUTING_JAVA_DIR>/build/libs/freerouting-current-executable.jar bytes=63288652 mtime=1788015935494 fixture=Issue508-DAC2020_bm01.dsn maxItems=100000 ripupPassNo=1 rules=- steps=1-8 neckWidthUm=0.0
