emshotton/copperroute/crates/copper-dsn/src/parser/library.rs

use copper_board::{Keepout, PackagePin, Padstack, PadstackId, Padstacks, equals_ignore_case};
use copper_geometry::{Area, Circle, IntVector, Shape, ShapeOps, TileShape, Vector};

use crate::coordinate_transform::CoordinateTransform;
use crate::error::DsnError;
use crate::format::format_double;
use crate::keyword::Keyword;
use crate::lexer::{DsnScanner, LexicalState, Token};
use crate::parser::dsn_file::read_on_off_scope;
use crate::parser::geometry::{
    self as shape, DsnLayer, DsnLayerStructure, DsnShape, ReadAreaScopeResult,
};
use crate::parser::placement::write_component_scope;
use crate::parser::scope_parameter::{ReadScopeParameter, WriteScopeParameter, skip_scope};

#[derive(Debug, Clone, PartialEq)]
pub struct DsnPinInfo {
    pub padstack_name: String,
    pub pin_name: String,
    pub rel_coor: [f64; 2],
    pub rotation: f64,
}

#[derive(Debug, Clone, PartialEq)]
pub struct DsnPackage {
    pub name: String,
    pub pin_info_arr: Vec<DsnPinInfo>,
    pub outline: Vec<DsnShape>,
    pub keepouts: Vec<ReadAreaScopeResult>,
    pub via_keepouts: Vec<ReadAreaScopeResult>,
    pub place_keepouts: Vec<ReadAreaScopeResult>,
    pub is_front: bool,
}

pub fn read_image_scope(
    scanner: &mut DsnScanner,
    layer_structure: Option<&DsnLayerStructure>,
) -> Result<Option<DsnPackage>, DsnError> {
    let mut is_front = true;
    let mut outline: Vec<DsnShape> = Vec::new();
    let mut keepouts: Vec<ReadAreaScopeResult> = Vec::new();
    let mut via_keepouts: Vec<ReadAreaScopeResult> = Vec::new();
    let mut place_keepouts: Vec<ReadAreaScopeResult> = Vec::new();
    let mut next_token = scanner.next_token()?;
    let Some(Token::Str(package_name)) = next_token.clone() else {
        return Ok(None);
    };
    scanner.set_scope_identifier(&package_name);
    let mut pin_info_list: Vec<DsnPinInfo> = Vec::new();
    loop {
        let prev_token = next_token;
        next_token = scanner.next_token()?;
        let Some(token) = next_token.clone() else {
            return Ok(None);
        };
        if token == Token::Close {
            break;
        }
        if prev_token == Some(Token::Open) {
            match token {
                Token::Kw(Keyword::Pin) => {
                    let Some(next_pin) = read_pin_info(scanner)? else {
                        return Ok(None);
                    };
                    pin_info_list.push(next_pin);
                }
                Token::Kw(Keyword::Side) => is_front = read_placement_side(scanner)?,
                Token::Kw(Keyword::Outline) => {
                    if let Some(current_shape) = shape::read_scope(scanner, layer_structure)? {
                        outline.push(current_shape);
                    }
                    next_token = scanner.next_token()?;
                    if next_token != Some(Token::Close) {
                        return Ok(None);
                    }
                }
                Token::Kw(Keyword::Keepout) => {
                    if let Some(keepout_area) =
                        shape::read_area_scope(scanner, layer_structure, false)?
                    {
                        keepouts.push(keepout_area);
                    }
                }
                Token::Kw(Keyword::ViaKeepout) => {
                    if let Some(keepout_area) =
                        shape::read_area_scope(scanner, layer_structure, false)?
                    {
                        via_keepouts.push(keepout_area);
                    }
                }
                Token::Kw(Keyword::PlaceKeepout) => {
                    if let Some(keepout_area) =
                        shape::read_area_scope(scanner, layer_structure, false)?
                    {
                        place_keepouts.push(keepout_area);
                    }
                }
                _ => {
                    skip_scope(scanner)?;
                }
            }
        }
    }
    Ok(Some(DsnPackage {
        name: package_name,
        pin_info_arr: pin_info_list,
        outline,
        keepouts,
        via_keepouts,
        place_keepouts,
        is_front,
    }))
}

fn read_pin_info(scanner: &mut DsnScanner) -> Result<Option<DsnPinInfo>, DsnError> {
    scanner.yybegin(LexicalState::Name);
    let mut next_token = scanner.next_token()?;
    let padstack_name = match &next_token {
        Some(Token::Str(s)) => s.clone(),
        Some(Token::Int(i)) => i.to_string(),
        _ => return Ok(None),
    };
    let mut rotation = 0.0;

    scanner.yybegin(LexicalState::Name);
    next_token = scanner.next_token()?;
    if next_token == Some(Token::Open) {
        next_token = scanner.next_token()?;
        if next_token == Some(Token::Kw(Keyword::Rotate)) {
            rotation = read_rotation(scanner)?;
        } else {
            skip_scope(scanner)?;
        }
        scanner.yybegin(LexicalState::Name);
        next_token = scanner.next_token()?;
    }
    let pin_name = match &next_token {
        Some(Token::Str(s)) => s.clone(),
        Some(Token::Int(i)) => i.to_string(),
        _ => return Ok(None),
    };

    let mut pin_coor = [0.0f64; 2];
    for coordinate in &mut pin_coor {
        next_token = scanner.next_token()?;
        match next_token {
            Some(Token::Float(f)) => *coordinate = f,
            #[allow(clippy::cast_precision_loss)]
            Some(Token::Int(i)) => *coordinate = i as f64,
            _ => return Ok(None),
        }
    }
    loop {
        let prev_token = next_token;
        next_token = scanner.next_token()?;
        let Some(token) = next_token.clone() else {
            return Ok(None);
        };
        if token == Token::Close {
            break;
        }
        if prev_token == Some(Token::Open) {
            if token == Token::Kw(Keyword::Rotate) {
                rotation = read_rotation(scanner)?;
            } else {
                skip_scope(scanner)?;
            }
        }
    }
    Ok(Some(DsnPinInfo {
        padstack_name,
        pin_name,
        rel_coor: pin_coor,
        rotation,
    }))
}

fn read_rotation(scanner: &mut DsnScanner) -> Result<f64, DsnError> {
    let next_string = scanner.next_string();
    let result = next_string.trim().parse::<f64>().unwrap_or(0.0);

    let _ = scanner.next_token()?;

    Ok(result)
}

fn read_placement_side(scanner: &mut DsnScanner) -> Result<bool, DsnError> {
    let next_token = scanner.next_token()?;
    let result = next_token != Some(Token::Kw(Keyword::Back));

    let _ = scanner.next_token()?;
    Ok(result)
}

pub fn write_package_scope(p: &mut WriteScopeParameter<'_>, board_package: &copper_board::Package) {
    p.file.start_scope_nl();
    p.file.write("image ");
    p.identifier_type.write(&board_package.name, &mut p.file);
    p.file.new_line();
    p.file.write("(side ");
    if board_package.is_front {
        p.file.write("front)");
    } else {
        p.file.write("back)");
    }
    #[allow(clippy::cast_possible_truncation, clippy::cast_possible_wrap)]
    for i in 0..board_package.pin_count() as i32 {
        let Some(current_pin) = board_package.get_pin(i) else {
            continue;
        };
        p.file.new_line();
        p.file.write("(pin ");
        let padstack_name = p
            .board
            .library
            .padstacks
            .get(current_pin.padstack_no)
            .map_or(String::new(), |padstack| padstack.name.clone());
        p.identifier_type.write(&padstack_name, &mut p.file);
        p.file.write(" ");
        let pin_name = current_pin.name.clone();
        p.identifier_type.write(&pin_name, &mut p.file);
        let rel_coor = p
            .coordinate_transform
            .board_to_dsn_vector(&current_pin.relative_location);
        for coordinate in rel_coor {
            p.file.write(" ");
            p.file.write(&format_double(coordinate));
        }
        let rotation = (current_pin.rotation_in_degree).round() as i32;
        if rotation != 0 {
            p.file.write("(rotate ");
            p.file.write(&rotation.to_string());
            p.file.write(")");
        }
        p.file.write(")");
    }
    for keepout in &board_package.keepouts {
        write_package_keepout(keepout, p, false);
    }
    for keepout in &board_package.via_keepouts {
        write_package_keepout(keepout, p, true);
    }
    if let Some(outline) = board_package.outline.as_ref() {
        for board_shape in outline {
            p.file.start_scope_nl();
            p.file.write("outline");
            if let Some(current_outline) = p
                .coordinate_transform
                .board_to_dsn_rel_shape(board_shape, DsnLayer::signal())
            {
                current_outline.write_scope(&mut p.file, &p.identifier_type);
            }
            p.file.end_scope();
        }
    }
    p.file.end_scope();
}

fn write_package_keepout(keepout: &Keepout, p: &mut WriteScopeParameter<'_>, is_via_keepout: bool) {
    let keepout_layer = if keepout.layer >= 0 {
        #[allow(clippy::cast_sign_loss)]
        let board_layer = &p.board.layer_structure().layers[keepout.layer as usize];
        DsnLayer::new(
            board_layer.name.clone(),
            keepout.layer,
            board_layer.is_signal,
        )
    } else {
        DsnLayer::signal()
    };
    let (boundary_shape, holes) = match &keepout.area {
        Area::Shape(s) => (s.clone(), Vec::new()),
        area => (area.get_border(), area.get_holes()),
    };
    p.file.start_scope_nl();
    if is_via_keepout {
        p.file.write("via_keepout");
    } else {
        p.file.write("keepout");
    }
    if let Some(dsn_shape) = p
        .coordinate_transform
        .board_to_dsn_shape(&boundary_shape, keepout_layer.clone())
    {
        dsn_shape.write_scope(&mut p.file, &p.identifier_type);
    }
    for hole in &holes {
        if let Some(dsn_hole) = p
            .coordinate_transform
            .board_to_dsn_shape(hole, keepout_layer.clone())
        {
            dsn_hole.write_hole_scope(&mut p.file, &p.identifier_type);
        }
    }
    p.file.end_scope();
}

pub fn write_component_placement_scope(p: &mut WriteScopeParameter<'_>, package_no: usize) {
    let board = p.board;
    let mut component_found = false;
    #[allow(clippy::cast_possible_truncation, clippy::cast_possible_wrap)]
    for i in 1..=board.components.count() as i32 {
        let current_component = board.components.get(i);
        if current_component.get_package() != package_no {
            continue;
        }
        let undeleted_item_found = board
            .get_items()
            .any(|item| item.component_id() == current_component.id);
        if !undeleted_item_found && current_component.is_placed() {
            continue;
        }
        if !component_found {
            let package_name = board.library.packages.get(package_no).name.clone();
            p.file.start_scope_nl();
            p.file.write("component ");
            p.identifier_type.write(&package_name, &mut p.file);
            component_found = true;
        }
        write_component_scope(p, current_component);
    }
    if component_found {
        p.file.end_scope();
    }
}

pub fn write_library_scope(p: &mut WriteScopeParameter<'_>) {
    p.file.start_scope_nl();
    p.file.write("library");

    let board = p.board;
    for i in 1..=board.library.packages.count() {
        let board_package = board.library.packages.get(i);
        write_package_scope(p, board_package);
    }

    for i in 1..=board.library.padstacks.count() {
        let Some(padstack) = board.library.padstacks.get(PadstackId(i)) else {
            continue;
        };
        write_padstack_scope(p, padstack);
    }

    p.file.end_scope();
}

pub fn write_padstack_scope(p: &mut WriteScopeParameter<'_>, padstack: &Padstack) {
    let layer_count = p.board.get_layer_count();
    let mut first_layer_no = 0usize;
    while first_layer_no < layer_count
        && padstack
            .get_shape(i32::try_from(first_layer_no).unwrap_or(i32::MAX))
            .is_none()
    {
        first_layer_no += 1;
    }
    let mut last_layer_no = i64::try_from(layer_count).unwrap_or(i64::MAX) - 1;
    while last_layer_no >= 0
        && padstack
            .get_shape(i32::try_from(last_layer_no).unwrap_or(i32::MAX))
            .is_none()
    {
        last_layer_no -= 1;
    }
    if first_layer_no >= layer_count || last_layer_no < 0 {
        return;
    }

    p.file.start_scope_nl();
    p.file.write("padstack ");
    let padstack_name = padstack.name.clone();
    p.identifier_type.write(&padstack_name, &mut p.file);
    #[allow(clippy::cast_possible_truncation)]
    for i in first_layer_no..=(last_layer_no as usize) {
        let Some(current_board_shape) = padstack.get_shape(i32::try_from(i).unwrap_or(i32::MAX))
        else {
            continue;
        };
        let board_layer = &p.board.layer_structure().layers[i];
        let current_layer = DsnLayer::new(
            board_layer.name.clone(),
            i32::try_from(i).unwrap_or(i32::MAX),
            board_layer.is_signal,
        );
        let current_shape = p
            .coordinate_transform
            .board_to_dsn_rel_shape(current_board_shape, current_layer);
        p.file.start_scope_nl();
        p.file.write("shape");
        if let Some(current_shape) = current_shape {
            current_shape.write_scope(&mut p.file, &p.identifier_type);
        }
        p.file.end_scope();
    }
    if !padstack.attach_allowed {
        p.file.new_line();
        p.file.write("(attach off)");
    }
    if padstack.placed_absolute {
        p.file.new_line();
        p.file.write("(absolute on)");
    }
    p.file.end_scope();
}

pub fn read_padstack_scope(
    scanner: &mut DsnScanner,
    layer_structure: &DsnLayerStructure,
    coordinate_transform: &CoordinateTransform,
    board_padstacks: &mut Padstacks,
) -> Result<bool, DsnError> {
    let mut is_drilllable = true;
    let mut placed_absolute = false;
    let mut shape_list: Vec<DsnShape> = Vec::new();
    let mut next_token = scanner.next_token()?;
    let Some(Token::Str(raw_name)) = next_token.clone() else {
        return Ok(false);
    };
    let padstack_name = strip_dot_digits(&raw_name);
    scanner.set_scope_identifier(&padstack_name);

    while next_token != Some(Token::Close) {
        let prev_token = next_token;
        next_token = scanner.next_token()?;
        if next_token.is_none() {
            return Ok(false);
        }
        if prev_token == Some(Token::Open) {
            match next_token {
                Some(Token::Kw(Keyword::Shape)) => {
                    if let Some(current_shape) = shape::read_scope(scanner, Some(layer_structure))?
                    {
                        shape_list.push(current_shape);
                    }
                    let mut current_next_token = scanner.next_token()?;
                    while current_next_token == Some(Token::Open) {
                        skip_scope(scanner)?;
                        current_next_token = scanner.next_token()?;
                    }
                    if current_next_token != Some(Token::Close) {
                        return Ok(false);
                    }
                }
                Some(Token::Kw(Keyword::Attach)) => is_drilllable = read_on_off_scope(scanner)?,
                Some(Token::Kw(Keyword::Absolute)) => placed_absolute = read_on_off_scope(scanner)?,
                _ => {
                    skip_scope(scanner)?;
                }
            }
        }
    }

    if board_padstacks.get_by_name(&padstack_name).is_some() {
        return Ok(true);
    }
    if shape_list.is_empty() {
        return Ok(true);
    }
    let mut padstack_shapes: Vec<Option<Shape>> = vec![None; layer_structure.layers.len()];
    for pad_shape in &shape_list {
        let mut padstack_shape = pad_shape
            .transform_to_board_rel(coordinate_transform)
            .and_then(to_convex_shape);
        if let Some(shape) = &padstack_shape
            && shape.dimension() < 2
        {
            let enlarged = offset_convex(shape, 1.0);
            padstack_shape = if enlarged.dimension() < 2 {
                None
            } else {
                Some(enlarged)
            };
        }

        let layer = pad_shape.layer();
        if *layer == DsnLayer::pcb() || *layer == DsnLayer::signal() {
            padstack_shapes.fill(padstack_shape);
        } else {
            let Some(shape_layer) = layer_structure.get_no(&layer.name) else {
                return Ok(false);
            };
            if shape_layer >= padstack_shapes.len() {
                return Ok(false);
            }
            padstack_shapes[shape_layer] = padstack_shape;
        }
    }
    board_padstacks.add(
        padstack_name,
        padstack_shapes,
        is_drilllable,
        placed_absolute,
    );
    Ok(true)
}

fn to_convex_shape(shape: Shape) -> Option<Shape> {
    match shape {
        Shape::Tile(_) | Shape::Circle(_) => Some(shape),
        Shape::Polygon(polygon) => {
            let hull = Shape::Polygon(polygon.convex_hull());
            let convex_shapes = hull.split_to_convex()?;
            let first = convex_shapes.first()?;
            Some(Shape::Tile(match first {
                TileShape::Simplex(simplex) => simplex.simplify(),
                other => other.clone(),
            }))
        }
    }
}

fn offset_convex(shape: &Shape, distance: f64) -> Shape {
    match shape {
        Shape::Tile(tile) => Shape::Tile(tile.offset(distance)),
        Shape::Circle(circle) => Shape::Circle(Circle::offset(circle, distance)),
        Shape::Polygon(_) => shape.clone(),
    }
}

fn are_package_pins_identical(pkg1: &copper_board::Package, p2: &[PackagePin]) -> bool {
    if pkg1.pin_count() != p2.len() {
        return false;
    }
    for (i, pin2) in p2.iter().enumerate() {
        #[allow(clippy::cast_possible_truncation, clippy::cast_possible_wrap)]
        let Some(pin1) = pkg1.get_pin(i as i32) else {
            return false;
        };
        if pin1.name != pin2.name {
            return false;
        }
        if pin1.padstack_no != pin2.padstack_no {
            return false;
        }
        let loc1 = pin1.relative_location.to_float();
        let loc2 = pin2.relative_location.to_float();
        if (loc1.x - loc2.x).abs() > 0.001 || (loc1.y - loc2.y).abs() > 0.001 {
            return false;
        }
        if (pin1.rotation_in_degree - pin2.rotation_in_degree).abs() > 0.001 {
            return false;
        }
    }
    true
}

pub fn read_library_scope(p: &mut ReadScopeParameter<'_>) -> Result<bool, DsnError> {
    let (Some(layer_structure), Some(coordinate_transform)) =
        (p.layer_structure.clone(), p.coordinate_transform)
    else {
        return Ok(false);
    };
    if p.board.is_none() {
        return Ok(false);
    }
    {
        let board_layer_structure = p
            .board
            .as_ref()
            .expect("checked above")
            .layer_structure()
            .clone();
        let board = p.board.as_mut().expect("checked above");
        board.library.padstacks = Padstacks::new(board_layer_structure);
    }
    let mut package_list: Vec<DsnPackage> = Vec::new();
    let mut next_token: Option<Token> = None;
    loop {
        let prev_token = next_token;
        next_token = p.scanner.next_token()?;
        let Some(token) = next_token.clone() else {
            return Ok(false);
        };
        if token == Token::Close {
            break;
        }
        if prev_token == Some(Token::Open) {
            match token {
                Token::Kw(Keyword::Padstack) => {
                    let board = p.board.as_mut().expect("checked above");
                    if !read_padstack_scope(
                        &mut p.scanner,
                        &layer_structure,
                        &coordinate_transform,
                        &mut board.library.padstacks,
                    )? {
                        return Ok(false);
                    }
                }
                Token::Kw(Keyword::Image) => {
                    let Some(current_package) =
                        read_image_scope(&mut p.scanner, Some(&layer_structure))?
                    else {
                        return Ok(false);
                    };
                    package_list.push(current_package);
                }
                _ => {
                    skip_scope(&mut p.scanner)?;
                }
            }
        }
    }

    let board = p.board.as_mut().expect("checked above");
    board.library.packages = copper_board::Packages::new();
    for mut current_package in package_list {
        let mut pins: Vec<PackagePin> = Vec::with_capacity(current_package.pin_info_arr.len());
        for pin_info in &current_package.pin_info_arr {
            let rel_x = (coordinate_transform.dsn_to_board(pin_info.rel_coor[0])).round() as i32;
            let rel_y = (coordinate_transform.dsn_to_board(pin_info.rel_coor[1])).round() as i32;
            let rel_coor = Vector::Int(IntVector::new(rel_x, rel_y));
            let cleaned_lookup_name = strip_dot_digits(&pin_info.padstack_name);
            let Some(board_padstack) = board.library.padstacks.get_by_name(&cleaned_lookup_name)
            else {
                return Ok(false);
            };
            pins.push(PackagePin::new(
                pin_info.pin_name.clone(),
                PadstackId(board_padstack.no),
                rel_coor,
                pin_info.rotation,
            ));
        }
        let mut outlines: Vec<Shape> = Vec::with_capacity(current_package.outline.len());
        let mut outline_widths: Vec<f64> = Vec::with_capacity(current_package.outline.len());
        let mut outline_is_closed: Vec<bool> = Vec::with_capacity(current_package.outline.len());

        for current_shape in &current_package.outline {
            let Some(board_shape) = current_shape.transform_to_board_rel(&coordinate_transform)
            else {
                continue;
            };
            outlines.push(board_shape);
            let path = match current_shape {
                DsnShape::Path(path) => Some((path.width, path.coordinate_arr.as_slice())),
                DsnShape::PolylinePath(path) => Some((path.width, path.coordinate_arr.as_slice())),
                _ => None,
            };
            if let Some((width, coords)) = path {
                outline_widths.push(width);
                outline_is_closed.push(path_is_closed(coords));
            } else {
                outline_widths.push(0.0);
                outline_is_closed.push(true);
            }
        }
        generate_missing_keepout_names("keepout_", &mut current_package.keepouts);
        generate_missing_keepout_names("via_keepout_", &mut current_package.via_keepouts);
        generate_missing_keepout_names("place_keepout_", &mut current_package.place_keepouts);
        let keepouts = board_keepouts(&current_package.keepouts, &coordinate_transform);
        let via_keepouts = board_keepouts(&current_package.via_keepouts, &coordinate_transform);
        let place_keepout_arr =
            board_keepouts(&current_package.place_keepouts, &coordinate_transform);

        // Placements refer to this exact image name. Numbered images may differ
        // in pad geometry or pin names, so do not renumber or merge them with
        // another explicitly named image.
        let base_package_name = current_package.name.clone();
        let mut suffix = 0u32;
        loop {
            let test_name = if suffix == 0 {
                base_package_name.clone()
            } else {
                format!("{base_package_name}::{suffix}")
            };
            let existing_matches = board
                .library
                .packages
                .get_by_name(&test_name, current_package.is_front)
                .filter(|existing| equals_ignore_case(&existing.name, &test_name))
                .map(|existing| are_package_pins_identical(existing, &pins));
            match existing_matches {
                None => {
                    board.library.packages.add(
                        test_name,
                        pins,
                        Some(outlines),
                        Some(outline_widths),
                        Some(outline_is_closed),
                        keepouts,
                        via_keepouts,
                        place_keepout_arr,
                        current_package.is_front,
                    );
                    break;
                }
                Some(true) => break,
                Some(false) => suffix += 1,
            }
        }
    }
    Ok(true)
}

fn path_is_closed(coords: &[f64]) -> bool {
    if coords.len() < 4 {
        return false;
    }
    coords[0] == coords[coords.len() - 2] && coords[1] == coords[coords.len() - 1]
}

fn board_keepouts(
    keepout_list: &[ReadAreaScopeResult],
    coordinate_transform: &CoordinateTransform,
) -> Vec<Keepout> {
    let mut result = Vec::with_capacity(keepout_list.len());
    for current_keepout in keepout_list {
        let Some(current_layer) = current_keepout
            .shape_list
            .first()
            .and_then(Option::as_ref)
            .map(DsnShape::layer)
        else {
            continue;
        };
        let layer_no = current_layer.no;
        let Some(current_area) =
            shape::transform_area_to_board_rel(&current_keepout.shape_list, coordinate_transform)
        else {
            continue;
        };
        result.push(Keepout::new(
            current_keepout.area_name.clone().unwrap_or_default(),
            current_area,
            layer_no,
        ));
    }
    result
}

fn generate_missing_keepout_names(keepout_type: &str, keepout_list: &mut [ReadAreaScopeResult]) {
    let all_names_existing = keepout_list.iter().all(|k| k.area_name.is_some());
    if all_names_existing {
        return;
    }
    for (i, current_keepout) in keepout_list.iter_mut().enumerate() {
        current_keepout.area_name = Some(format!("{keepout_type}{}", i + 1));
    }
}

pub(crate) fn strip_dot_digits(name: &str) -> String {
    let mut out = String::with_capacity(name.len());
    let mut chars = name.chars().peekable();
    while let Some(c) = chars.next() {
        if c == '.' && chars.peek().is_some_and(char::is_ascii_digit) {
            while chars.peek().is_some_and(char::is_ascii_digit) {
                chars.next();
            }
            continue;
        }
        out.push(c);
    }
    out
}

#[cfg(test)]
mod tests {
    use super::*;

    #[test]
    fn strip_dot_digits_removes_every_dotted_number() {
        assert_eq!(strip_dot_digits("Pad_1358_um"), "Pad_1358_um");
        assert_eq!(strip_dot_digits("Pad.12"), "Pad");
        assert_eq!(strip_dot_digits("a.1b.23c"), "abc");
        assert_eq!(strip_dot_digits("F.Cu"), "F.Cu");
        assert_eq!(strip_dot_digits("a."), "a.");
        assert_eq!(strip_dot_digits(""), "");
        assert_eq!(
            strip_dot_digits("Via[0-1]_1016:485.7_um"),
            "Via[0-1]_1016:485_um"
        );
        assert_eq!(strip_dot_digits("a.\u{0661}"), "a.\u{0661}");
        assert_eq!(strip_dot_digits("PAD."), "PAD.");
        assert_eq!(strip_dot_digits("µ.7x"), "µx");
    }

    #[test]
    fn generate_missing_keepout_names_renames_all_or_none() {
        let mut list = vec![
            ReadAreaScopeResult {
                shape_list: Vec::new(),
                clearance_class_name: None,
                area_name: Some("kept".to_string()),
            },
            ReadAreaScopeResult {
                shape_list: Vec::new(),
                clearance_class_name: None,
                area_name: None,
            },
        ];
        generate_missing_keepout_names("keepout_", &mut list);
        assert_eq!(list[0].area_name.as_deref(), Some("keepout_1"));
        assert_eq!(list[1].area_name.as_deref(), Some("keepout_2"));

        let mut all_named = vec![ReadAreaScopeResult {
            shape_list: Vec::new(),
            clearance_class_name: None,
            area_name: Some("kept".to_string()),
        }];
        generate_missing_keepout_names("keepout_", &mut all_named);
        assert_eq!(all_named[0].area_name.as_deref(), Some("kept"));
    }
}
