emshotton/copperroute/crates/copper-dsn/src/parser/mod.rs

pub mod autoroute_settings;
pub mod dsn_file;
pub mod geometry;
pub mod header;
pub mod library;
pub mod network;
pub mod part_library;
pub mod placement;
pub mod scope_parameter;
pub mod structure;
pub mod wiring;

pub use autoroute_settings::DsnRouterSettings;
pub use geometry::{
    DsnCircle, DsnLayer, DsnLayerStructure, DsnPolygon, DsnPolygonPath, DsnPolylinePath,
    DsnRectangle, DsnShape, ReadAreaScopeResult,
};
